20mup/jurassic-rescue-robot/code/MREN_303_Pico_W_Wifi_Gamepad_Input_Battery_Read_Update__1_.py

# MREN 303 Pico W Wifi Gamepad Input
# Written For MREN 303

from inputs import get_gamepad #IMPORTANT NOTE, ONLY WORKS WITH GAMEPAD X_D SWITCH SET TO X
import socket

UDP_IP = "192.168.50.69" #Change to Match IP Of Target Pico w
UDP_PORT = 8888

MESSAGE = b"Hello, World!" #This b"Hello World!" encodes the Hello World! string to a series of bytes which can be sent over UDP

def connect():

    print("UDP target IP: %s" % UDP_IP)
    print("UDP target port: %s" % UDP_PORT)
    print("message: %s" % MESSAGE)

    #The following line establishes a connection with the Pico W MicroController

    sock = socket.socket(socket.AF_INET, # Internet
                        socket.SOCK_DGRAM) # UDP
    sock.sendto(MESSAGE, (UDP_IP, UDP_PORT))
    sock.settimeout(2.0)
    sent=False
    return sock

def main():
    sock = connect()

    while 1:
        events = get_gamepad()
        for event in events:
            if(event.state != 0):
                print("code:" , event.code, "state:" ,event.state)
            #BUTTONS
            #Recoding As Labelled On Controller
            #event.state 1 is button press, for button release use event.state 0
            if(event.code == "BTN_SOUTH" and event.state == 1):
                payload= b"A Button Press"
                sock.sendto(payload, (UDP_IP, UDP_PORT));
                sent = True
            if(event.code == "BTN_EAST" and event.state == 1):
                payload= b"B Button Press"
                sock.sendto(payload, (UDP_IP, UDP_PORT));
                sent=True
            if(event.code == "BTN_NORTH" and event.state == 1):
                payload= b"Y Button Press"
                sock.sendto(payload, (UDP_IP, UDP_PORT));
                sent=True
            if(event.code == "BTN_WEST" and event.state == 1):
                payload= b"X Button Press"
                sock.sendto(payload, (UDP_IP, UDP_PORT));
                sent=True
            if(event.code == "BTN_TL" and event.state == 1):
                payload= b"LB Button Press"
                sock.sendto(payload, (UDP_IP, UDP_PORT));
                sent=True
            if(event.code == "BTN_TR" and event.state == 1):
                payload= b"RB Button Press"
                sock.sendto(payload, (UDP_IP, UDP_PORT));
                sent=True
            if(event.code == "BTN_THUMBL" and event.state == 1):
                payload= b"L Stick Press"
                sock.sendto(payload, (UDP_IP, UDP_PORT));
                sent=True
            if(event.code == "BTN_THUMBR" and event.state == 1):
                payload= b"R Stick Press"
                sock.sendto(payload, (UDP_IP, UDP_PORT));
                sent=True
            if(event.code == "BTN_START" and event.state == 1):
                payload= b"Back Press"
                sock.sendto(payload, (UDP_IP, UDP_PORT));
                sent=True
            if(event.code == "BTN_SELECT" and event.state == 1):
                payload= b"Start Press"
                sock.sendto(payload, (UDP_IP, UDP_PORT));
                sent=True

            #ABS
            #These inputs give a range of values and are affected by the mode select button, please be aware of this when troubleshooting
            if(event.code == "ABS_Z"):
                payload = "L Trigger Value {}".format(event.state)
                payload = payload.encode("UTF-8")
                sock.sendto(payload, (UDP_IP, UDP_PORT));
                sent=True
            if(event.code == "ABS_RZ"):
                payload = "R Trigger Value {}".format(event.state)
                payload = payload.encode("UTF-8")
                sock.sendto(payload, (UDP_IP, UDP_PORT));
                sent=True
            if(event.code == "ABS_HAT0X"):
                if event.state == 1:
                    payload = b"Right DPad Press"
                if event.state == -1:
                    payload = b"Left DPad Press"
                sock.sendto(payload, (UDP_IP, UDP_PORT));
                sent=True
            if(event.code == "ABS_HAT0Y"):
                if event.state == 1:
                    payload = b"Down DPad Press"
                if event.state == -1:
                    payload = b"Up DPad Press"
                sock.sendto(payload, (UDP_IP, UDP_PORT));
                sent=True

            if(event.code == "ABS_Y"):
                value = round(event.state/128) #Reducing Resolution
                if value > 255 : value = value -1 #Keep value between 255 and -255
                if value < -255 : value = value + 1
                payload = "L Stick Y Value {}".format(value)
                payload = payload.encode("ascii")
                sock.sendto(payload, (UDP_IP, UDP_PORT));
                sent=True
            if(event.code == "ABS_X"):
                value = round(event.state/128) #Reducing Resolution
                if value > 255 : value = value -1 #Keep value between 255 and -255
                if value < -255 : value = value + 1
                payload = "L Stick X Value {}".format(value)
                payload = payload.encode("ascii")
                sock.sendto(payload, (UDP_IP, UDP_PORT));
                sent=True
            if(event.code == "ABS_RY"):
                value = round(event.state/128) #Reducing Resolution
                if value > 255 : value = value -1 #Keep value between 255 and -255
                if value < -255 : value = value + 1
                payload = "R Stick Y Value {}".format(value)
                payload = payload.encode("ascii")
                sock.sendto(payload, (UDP_IP, UDP_PORT));
                sent=True
            if(event.code == "ABS_RX"):
                value = round(event.state/128) #Reducing Resolution
                if value > 255 : value = value -1 #Keep value between 255 and -255
                if value < -255 : value = value + 1
                payload = "R Stick X Value {}".format(value)
                payload = payload.encode("ascii")
                sock.sendto(payload, (UDP_IP, UDP_PORT));
                sent=True

        if (sent):
            try:
                response = sock.recv(1024)
            except socket.timeout:
                print("timeout")
                sock = connect()
                continue
            except:
                print("Error USER'S TRY EXCEPT")
                return
            else:
                print(response.decode())
        sent=False


if __name__ == "__main__":
    main()
